feklee/stm/approach/2016-03-20+01_electronics/bias_voltage_regulator.jpg

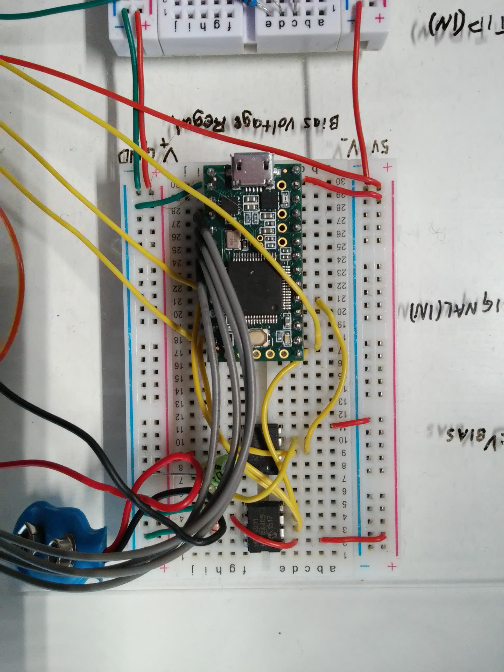
approach/2016-03-20+01_electronics/bias_voltage_regulator.jpg
