feklee/stm/approach/2016-03-20+01_electronics/piezo_controller.jpg

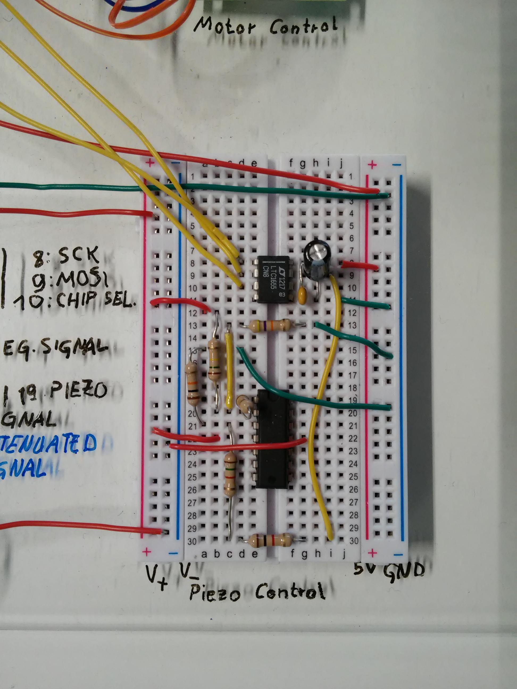
approach/2016-03-20+01_electronics/piezo_controller.jpg
