feklee/stm/approach/2016-04-09+02_electronics/motor_control.jpg

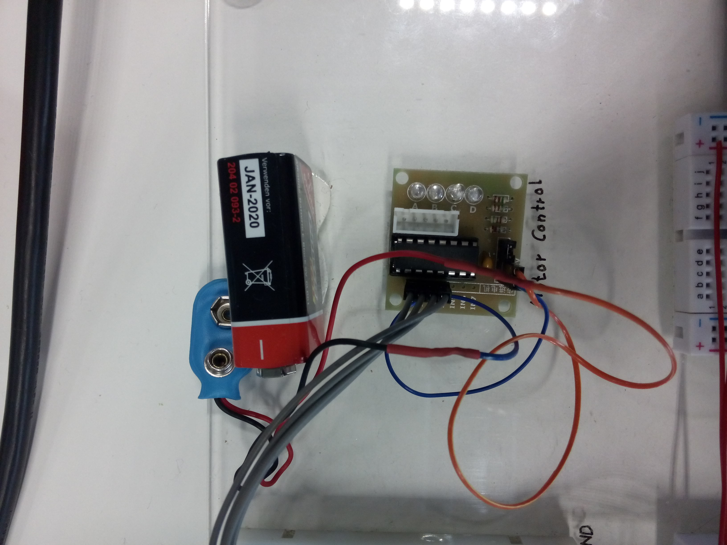
approach/2016-04-09+02_electronics/motor_control.jpg
