feklee/stm/approach/2016-04-09+02_electronics/piezo_controller.jpg

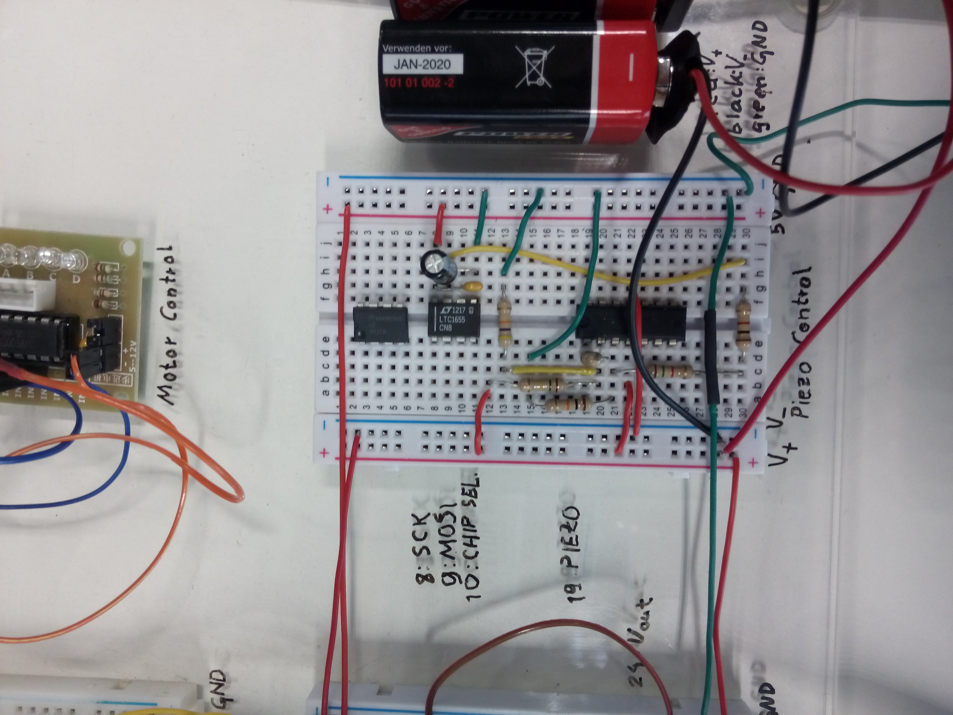
approach/2016-04-09+02_electronics/piezo_controller.jpg
