feklee/stm/new_software/microcontroller/TipPositionLog.hpp

#pragma once

class TipPositionLog {
  struct Entry {
    uint8_t x;
    uint8_t y;
    uint16_t z; // piezo position
    uint16_t currentSignal; // 0xffff/3.3 V
    uint32_t time; // µs since program start
  };

  static const int size_ = 1000;
  Entry entries_[size_];
  int head_ = 0;
  void print();

public:
  void flush();
  void add(uint8_t, uint8_t, uint16_t, uint16_t);
};
