feklee/stm/new_software/microcontroller/PiezoPlayMode.cpp

#include <Arduino.h>
#include "PiezoPlayMode.hpp"

PiezoPlayMode::PiezoPlayMode(Piezo &piezo) : piezo_(piezo) {}

const char *PiezoPlayMode::name() {
  return "piezoPlay";
}

bool PiezoPlayMode::step() {
  piezo_.play(250);
  return true;
}
