feklee/stm/new_software/microcontroller/BiasVoltage.hpp

#pragma once

#include <Arduino.h>

class BiasVoltage {
  const uint8_t chipSelectPin_ = 8;
  const uint8_t measurePin_ = A3;
  void setFactor(float);

public:
  void setup();
  void set(float);
  float measuredValue();
  void print();
};
