feklee/stm/new_software/microcontroller/util.hpp

#pragma once

#include <Arduino.h>

void printError(const char *);
float voltFromInteger(uint16_t);
uint16_t integerFromVolt(float);
float readVoltage(uint8_t);
template <typename T> void printValue(const char *, T);
unsigned long elapsedTime(unsigned long, unsigned long);
